theohg/PD240W/src/utils/tps_eeprom_loader.cpp

/**
 * @file tps_eeprom_loader.cpp
 * @brief Implementation of the EEPROM flashing logic for TPS26750.
 *
 * Uses I2C1 on GPIO 14 (SDA) / GPIO 15 (SCL) to communicate with the
 * CAT24C512 EEPROM that stores the TPS26750 configuration patch.
 */

#include "tps_eeprom_loader.h"
#include "pico/stdlib.h"
#include "hardware/i2c.h"
#include "hardware/gpio.h"
#include "utils/logging.h"
#include <string.h>
#include <algorithm>

// =============================================================================
// External Data References (from full_flash_c_config.c)
// =============================================================================

extern "C" {
    extern const char tps25750x_fullFlash_i2c_array[];
    extern int gSizeFullFlashArray;
}

// =============================================================================
// Private Helper Functions
// =============================================================================

// Tracks whether I2C1 is currently claimed for EEPROM access so the init/deinit
// helpers are idempotent. Several no-flash workflow paths call eepromDeinit()
// and then cleanup() calls it again; without this the SDK i2c_deinit + GPIO
// reset would run twice on the same idle bus.
static bool s_i2c_active = false;

/**
 * @brief Initialize I2C1 on GPIO 14/15 for EEPROM access.
 */
static void eeprom_i2c_init() {
    if (s_i2c_active) return;
    s_i2c_active = true;
    // Initialize I2C1 peripheral
    i2c_init(EEPROM_I2C_INST, EEPROM_I2C_SPEED_HZ);

    // Configure GPIO pins for I2C function
    gpio_set_function(EEPROM_I2C_SDA_PIN, GPIO_FUNC_I2C);
    gpio_set_function(EEPROM_I2C_SCL_PIN, GPIO_FUNC_I2C);

    // Enable internal pull-ups (external pull-ups should also be present)
    gpio_pull_up(EEPROM_I2C_SDA_PIN);
    gpio_pull_up(EEPROM_I2C_SCL_PIN);

    LOG_INFO("[EEPROM] I2C1 initialized on GPIO %d (SDA) / GPIO %d (SCL) @ %d Hz",
             EEPROM_I2C_SDA_PIN, EEPROM_I2C_SCL_PIN, EEPROM_I2C_SPEED_HZ);
}

/**
 * @brief Deinitialize I2C1 to release resources.
 */
static void eeprom_i2c_deinit() {
    if (!s_i2c_active) return;
    s_i2c_active = false;
    i2c_deinit(EEPROM_I2C_INST);

    // Reset GPIO pins to default state (input, no pulls)
    gpio_set_function(EEPROM_I2C_SDA_PIN, GPIO_FUNC_NULL);
    gpio_set_function(EEPROM_I2C_SCL_PIN, GPIO_FUNC_NULL);
    gpio_disable_pulls(EEPROM_I2C_SDA_PIN);
    gpio_disable_pulls(EEPROM_I2C_SCL_PIN);

    LOG_INFO("[EEPROM] I2C1 deinitialized");
}

/**
 * @brief Scan I2C bus and print found devices (for debugging)
 *
 * Kept as a bench tool: not called in normal flows, so [[maybe_unused]] keeps
 * it compiled and warning-free until someone wires it into a debug path.
 */
[[maybe_unused]] static void eeprom_i2c_scan() {
    LOG_INFO("[EEPROM] Scanning I2C1 bus...");
    int found = 0;
    for (uint8_t addr = 0x08; addr < 0x78; addr++) {
        uint8_t dummy;
        // Try to read 1 byte - if device ACKs, it's present
        int ret = i2c_read_blocking(EEPROM_I2C_INST, addr, &dummy, 1, false);
        if (ret >= 0) {
            LOG_INFO("[EEPROM]   Found device at 0x%02X", addr);
            found++;
        }
    }
    LOG_INFO("[EEPROM] Scan complete: %d device(s) found", found);
}

/**
 * @brief Probe for EEPROM device presence on I2C bus.
 * @return true if device ACKs, false if NACK or timeout
 */
static bool eeprom_probe_device() {
    // Simple probe: write address bytes and check for ACK
    // This mimics what i2cdetect does
    uint8_t addr_buf[2] = {0x00, 0x00};  // EEPROM memory address 0x0000

    // Use blocking version for probe - more reliable
    int ret = i2c_write_blocking(EEPROM_I2C_INST, EEPROM_I2C_ADDR, addr_buf, 2, false);

    LOG_DEBUG("[EEPROM] Probe result: ret=%d", ret);

    // ret == 2 means 2 bytes written successfully (device ACKed)
    // ret < 0 means error (NACK or bus issue)
    return (ret == 2);
}

/**
 * @brief Write a single page-aligned chunk (up to the next EEPROM page boundary,
 *        capped at @p len) starting at @p mem_addr.
 *
 * Shared by the blocking eeprom_write_block() and the non-blocking
 * eepromFlashStep(): both need the same page-boundary math and I2C packet layout;
 * only the wait-for-write-cycle sequencing differs (blocking sleep vs. timer), so
 * that is left to the caller. Returns the raw i2c_write_timeout_us() result and,
 * on any non-negative return, stores the number of data bytes written in
 * @p out_chunk.
 */
static int eeprom_write_page_chunk(uint16_t mem_addr, const uint8_t* data, size_t len,
                                   size_t* out_chunk) {
    uint16_t page_offset = mem_addr % EEPROM_PAGE_SIZE;
    size_t chunk_size = std::min((size_t)(EEPROM_PAGE_SIZE - page_offset), len);

    // Prepare I2C packet: [Addr High] [Addr Low] [Data...]
    uint8_t buffer[EEPROM_PAGE_SIZE + 2];
    buffer[0] = (mem_addr >> 8) & 0xFF;
    buffer[1] = mem_addr & 0xFF;
    memcpy(&buffer[2], data, chunk_size);

    *out_chunk = chunk_size;
    return i2c_write_timeout_us(EEPROM_I2C_INST, EEPROM_I2C_ADDR, buffer,
                                chunk_size + 2, false, EEPROM_I2C_TIMEOUT_US);
}

/**
 * @brief Writes a block of data to the EEPROM handling page boundaries.
 * @param mem_addr  Starting EEPROM memory address
 * @param data      Pointer to data buffer
 * @param len       Number of bytes to write
 * @return true on success, false on I2C error
 */
static bool eeprom_write_block(uint16_t mem_addr, const uint8_t* data, size_t len) {
    size_t written = 0;
    while (written < len) {
        size_t chunk_size = 0;
        int ret = eeprom_write_page_chunk(mem_addr, &data[written], len - written, &chunk_size);

        if (ret == PICO_ERROR_GENERIC) {
            LOG_ERROR("[EEPROM] I2C write NACK at 0x%04X", mem_addr);
            return false;
        } else if (ret == PICO_ERROR_TIMEOUT) {
            LOG_ERROR("[EEPROM] I2C write TIMEOUT at 0x%04X", mem_addr);
            return false;
        } else if (ret < 0) {
            LOG_ERROR("[EEPROM] I2C write error at 0x%04X (ret=%d)", mem_addr, ret);
            return false;
        }

        // Wait for EEPROM internal write cycle to complete
        sleep_ms(EEPROM_WRITE_DELAY_MS);

        // Advance pointers
        mem_addr += chunk_size;
        written += chunk_size;
    }

    return true;
}

/**
 * @brief Reads a block of data from the EEPROM.
 * @param mem_addr  Starting EEPROM memory address
 * @param dest      Destination buffer
 * @param len       Number of bytes to read
 * @return true on success, false on I2C error
 */
static bool eeprom_read_block(uint16_t mem_addr, uint8_t* dest, size_t len) {
    uint8_t addr_buf[2];
    addr_buf[0] = (mem_addr >> 8) & 0xFF;
    addr_buf[1] = mem_addr & 0xFF;

    // Write the address we want to read from (with repeated start)
    int ret = i2c_write_timeout_us(EEPROM_I2C_INST, EEPROM_I2C_ADDR, addr_buf, 2, true, EEPROM_I2C_TIMEOUT_US);
    if (ret == PICO_ERROR_TIMEOUT) {
        LOG_ERROR("[EEPROM] I2C address write TIMEOUT at 0x%04X", mem_addr);
        return false;
    } else if (ret < 0) {
        LOG_ERROR("[EEPROM] I2C address write error at 0x%04X (ret=%d)", mem_addr, ret);
        return false;
    }

    // Read the data with timeout
    ret = i2c_read_timeout_us(EEPROM_I2C_INST, EEPROM_I2C_ADDR, dest, len, false, EEPROM_I2C_TIMEOUT_US);
    if (ret == PICO_ERROR_TIMEOUT) {
        LOG_ERROR("[EEPROM] I2C read TIMEOUT at 0x%04X", mem_addr);
        return false;
    } else if (ret < 0) {
        LOG_ERROR("[EEPROM] I2C read error at 0x%04X (ret=%d)", mem_addr, ret);
        return false;
    }

    return true;
}

/**
 * @brief Check if EEPROM already contains the correct data.
 * @param fw_data   Pointer to firmware data
 * @param fw_size   Size of firmware data
 * @return true if EEPROM matches firmware exactly
 */
static bool eeprom_already_programmed(const uint8_t* fw_data, size_t fw_size) {
    uint8_t read_buffer[128];
    size_t checked = 0;

    // Quick check: Read first 128 bytes to detect obvious mismatch early
    if (!eeprom_read_block(0, read_buffer, sizeof(read_buffer))) {
        LOG_WARN("[EEPROM] Quick check read failed");
        return false;
    }
    if (memcmp(fw_data, read_buffer, std::min(sizeof(read_buffer), fw_size)) != 0) {
        LOG_INFO("[EEPROM] Header mismatch - needs programming");
        return false;
    }
    LOG_INFO("[EEPROM] Header matches, checking full image...");
    checked = sizeof(read_buffer);

    // Full verification with progress
    while (checked < fw_size) {
        size_t chunk = std::min(sizeof(read_buffer), fw_size - checked);

        if (!eeprom_read_block(checked, read_buffer, chunk)) {
            LOG_WARN("[EEPROM] Read failed at 0x%04X during check", checked);
            return false;  // Read failed, assume not programmed
        }

        if (memcmp(&fw_data[checked], read_buffer, chunk) != 0) {
            LOG_INFO("[EEPROM] Mismatch at 0x%04X - needs programming", checked);
            return false;  // Mismatch found
        }

        checked += chunk;

        // Progress every 4KB
        if ((checked % 4096) == 0) {
            LOG_INFO("[EEPROM] Checking... %u / %u bytes", checked, fw_size);
        }
    }

    return true;  // All bytes match
}

/**
 * @brief Check if EEPROM appears to be empty (all 0xFF or all 0x00).
 * @return true if first 128 bytes are all 0xFF or all 0x00
 */
static bool eeprom_is_empty() {
    uint8_t read_buffer[128];
    if (!eeprom_read_block(0, read_buffer, sizeof(read_buffer))) {
        return false;  // Can't read, assume not empty
    }

    bool all_ff = true;
    bool all_00 = true;
    for (size_t i = 0; i < sizeof(read_buffer); i++) {
        if (read_buffer[i] != 0xFF) all_ff = false;
        if (read_buffer[i] != 0x00) all_00 = false;
    }

    return all_ff || all_00;
}

static EepromFlashStatus setFlashError(EepromFlashSession* session, const char* error_message) {
    if (session) {
        session->error_message = error_message;
    }
    return EepromFlashStatus::ERROR;
}

// =============================================================================
// Public Runtime API
// =============================================================================

bool eepromInit() {
    eeprom_i2c_init();
    sleep_ms(50);  // Allow bus to stabilize
    return true;
}

void eepromDeinit() {
    eeprom_i2c_deinit();
}

bool eepromProbe() {
    return eeprom_probe_device();
}

size_t eepromGetFirmwareSize() {
    return (size_t)gSizeFullFlashArray;
}

bool eepromFlashBegin(EepromFlashSession* session) {
    if (!session) {
        return false;
    }

    session->fw_data = nullptr;
    session->fw_size = 0;
    session->write_offset = 0;
    session->verify_offset = 0;
    session->next_action_time = get_absolute_time();
    session->waiting_for_write_cycle = false;
    session->verify_announced = false;
    session->error_message = nullptr;

    if (gSizeFullFlashArray <= 0 || (size_t)gSizeFullFlashArray > EEPROM_TOTAL_SIZE) {
        session->error_message = "Invalid image";
        LOG_ERROR("[EEPROM] Invalid firmware size: %d bytes", gSizeFullFlashArray);
        return false;
    }

    if (!eeprom_probe_device()) {
        session->error_message = "EEPROM not found";
        LOG_ERROR("[EEPROM] Device not found at 0x%02X", EEPROM_I2C_ADDR);
        return false;
    }

    session->fw_data = reinterpret_cast<const uint8_t*>(tps25750x_fullFlash_i2c_array);
    session->fw_size = (size_t)gSizeFullFlashArray;

    LOG_INFO("[EEPROM] Flash session started for %u bytes", session->fw_size);
    return true;
}

EepromFlashStatus eepromFlashStep(EepromFlashSession* session,
                                  EepromProgressCallback callback,
                                  void* user_data) {
    if (!session || !session->fw_data || session->fw_size == 0) {
        return setFlashError(session, "Flash session invalid");
    }

    if (session->waiting_for_write_cycle) {
        if (absolute_time_diff_us(session->next_action_time, get_absolute_time()) < 0) {
            return EepromFlashStatus::IN_PROGRESS;
        }
        session->waiting_for_write_cycle = false;
    }

    if (session->write_offset < session->fw_size) {
        uint16_t mem_addr = session->write_offset;
        size_t chunk_size = 0;
        int ret = eeprom_write_page_chunk(mem_addr, &session->fw_data[session->write_offset],
                                          session->fw_size - session->write_offset, &chunk_size);
        if (ret == PICO_ERROR_TIMEOUT) {
            LOG_ERROR("[EEPROM] Write timeout at 0x%04X", mem_addr);
            return setFlashError(session, "Write timeout");
        }
        if (ret < 0) {
            LOG_ERROR("[EEPROM] Write failed at 0x%04X (ret=%d)", mem_addr, ret);
            return setFlashError(session, "Write failed");
        }

        session->write_offset += chunk_size;
        session->waiting_for_write_cycle = true;
        session->next_action_time = make_timeout_time_ms(EEPROM_WRITE_DELAY_MS);

        if (callback) {
            uint8_t progress = (uint8_t)((session->write_offset * 100) / session->fw_size);
            callback(0, progress, user_data);
        }

        if ((session->write_offset % 1024) == 0 || session->write_offset == session->fw_size) {
            LOG_INFO("[EEPROM] Writing... %u / %u bytes", session->write_offset, session->fw_size);
        }

        return EepromFlashStatus::IN_PROGRESS;
    }

    if (!session->verify_announced) {
        session->verify_announced = true;
        LOG_INFO("[EEPROM] Phase 2: Verifying...");
        if (callback) {
            callback(1, 0, user_data);
        }
        return EepromFlashStatus::IN_PROGRESS;
    }

    if (session->verify_offset < session->fw_size) {
        uint8_t read_buffer[128];
        size_t chunk = std::min(sizeof(read_buffer), session->fw_size - session->verify_offset);

        if (!eeprom_read_block(session->verify_offset, read_buffer, chunk)) {
            LOG_ERROR("[EEPROM] Verification read failed at 0x%04X", session->verify_offset);
            return setFlashError(session, "Verify read failed");
        }

        if (memcmp(&session->fw_data[session->verify_offset], read_buffer, chunk) != 0) {
            LOG_ERROR("[EEPROM] Verification mismatch at 0x%04X", session->verify_offset);
            return setFlashError(session, "Verify mismatch");
        }

        session->verify_offset += chunk;

        if (callback) {
            uint8_t progress = (uint8_t)((session->verify_offset * 100) / session->fw_size);
            callback(1, progress, user_data);
        }

        if ((session->verify_offset % 4096) == 0 || session->verify_offset == session->fw_size) {
            LOG_INFO("[EEPROM] Verifying... %u / %u bytes", session->verify_offset, session->fw_size);
        }

        if (session->verify_offset >= session->fw_size) {
            LOG_INFO("[EEPROM] Verification complete - SUCCESS!");
            return EepromFlashStatus::SUCCESS;
        }
    }

    return EepromFlashStatus::IN_PROGRESS;
}

EepromCompareResult eepromCompare() {
    // Check firmware size sanity
    if (gSizeFullFlashArray <= 0 || (size_t)gSizeFullFlashArray > EEPROM_TOTAL_SIZE) {
        LOG_ERROR("[EEPROM] Invalid firmware size: %d bytes", gSizeFullFlashArray);
        return EepromCompareResult::READ_ERROR;
    }

    // Probe for device
    if (!eeprom_probe_device()) {
        LOG_ERROR("[EEPROM] Device not found at 0x%02X", EEPROM_I2C_ADDR);
        return EepromCompareResult::NO_DEVICE;
    }

    const uint8_t* fw_data = reinterpret_cast<const uint8_t*>(tps25750x_fullFlash_i2c_array);

    // Check if empty first
    if (eeprom_is_empty()) {
        LOG_INFO("[EEPROM] EEPROM appears to be empty");
        return EepromCompareResult::EMPTY;
    }

    // Compare against firmware
    if (eeprom_already_programmed(fw_data, gSizeFullFlashArray)) {
        LOG_INFO("[EEPROM] EEPROM matches firmware exactly");
        return EepromCompareResult::IDENTICAL;
    }

    LOG_INFO("[EEPROM] EEPROM has different configuration");
    return EepromCompareResult::DIFFERENT;
}

bool eepromEraseAll() {
    eeprom_i2c_init();
    sleep_ms(50);  // Allow bus to stabilize

    bool ok = eeprom_probe_device();
    if (!ok) {
        LOG_ERROR("[EEPROM] Erase: device not found at 0x%02X", EEPROM_I2C_ADDR);
        eeprom_i2c_deinit();
        return false;
    }

    // Only the config-image region needs to be invalidated for the TPS to reject
    // it; clamp to the firmware size when known, else the full device.
    size_t erase_size = (gSizeFullFlashArray > 0 && (size_t)gSizeFullFlashArray <= EEPROM_TOTAL_SIZE)
                            ? (size_t)gSizeFullFlashArray
                            : EEPROM_TOTAL_SIZE;

    uint8_t blank[EEPROM_PAGE_SIZE];
    memset(blank, 0xFF, sizeof(blank));

    size_t offset = 0;
    while (offset < erase_size) {
        size_t chunk = std::min(sizeof(blank), erase_size - offset);
        if (!eeprom_write_block((uint16_t)offset, blank, chunk)) {
            LOG_ERROR("[EEPROM] Erase failed at 0x%04X", (unsigned)offset);
            eeprom_i2c_deinit();
            return false;
        }
        offset += chunk;
        if ((offset % 4096) == 0 || offset == erase_size) {
            LOG_INFO("[EEPROM] Erasing... %u / %u bytes", (unsigned)offset, (unsigned)erase_size);
        }
    }

    LOG_INFO("[EEPROM] Erased %u bytes to 0xFF - power-cycle to boot TPS into PTCH",
             (unsigned)erase_size);
    eeprom_i2c_deinit();
    return true;
}
